Blevene/Labscon-Badge-2022/bmp/bitcoin.bmp

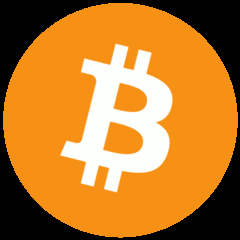
bmp/bitcoin.bmp
