Blevene/Labscon-Badge-2022/bmp/jags_cwc.bmp

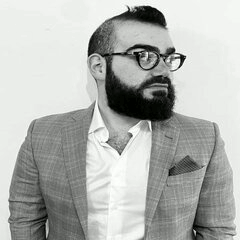
bmp/jags_cwc.bmp
